SamuelHudec/van-fox/doc/1.jpeg

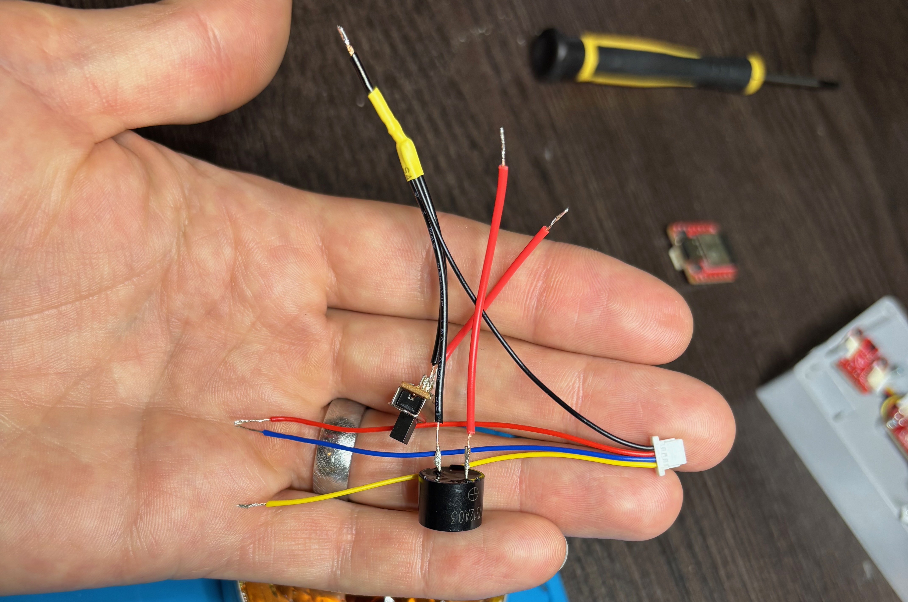
doc/1.jpeg
